apedersen00/tt6581/pcb/power.kicad_sch

## KiCad design pcb/power.kicad_sch (2026-03-07, an earlier design)

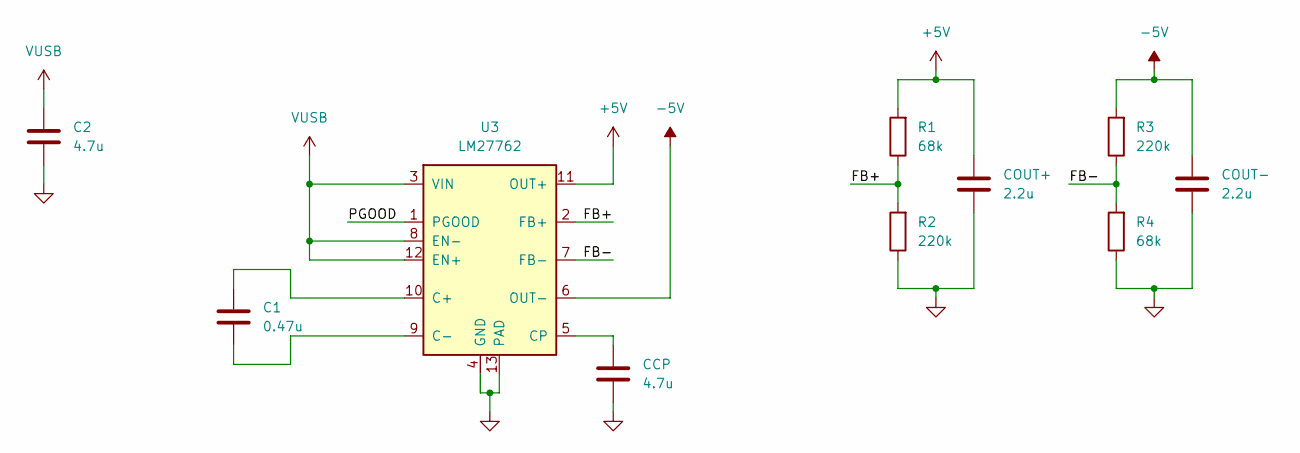
[picture p2: schematic power.kicad_sch]

Parts:
C1: 0.47u
C2: 4.7u
CCP: 4.7u
COUT+: 2.2u
COUT-: 2.2u
R1, R4: 68k
R2, R3: 220k
U3: LM27762; WSON-12-1EP_3x2mm_P0.5mm_EP1x2.65_ThermalVias

Connections:
+5V: COUT+.1, R1.2, U3.11 (OUT+)
-5V: COUT-.1, R3.2, U3.6 (OUT-)
FB+: R1.1, R2.2, U3.2 (FB+)
FB-: R3.1, R4.2, U3.7 (FB-)
GND: C2.2, CCP.2, COUT+.2, COUT-.2, R2.1, R4.1, U3.4 (GND), U3.13 (PAD)
unnamed: C1.1, U3.10 (C+)
unnamed: C1.2, U3.9 (C-)
unnamed: CCP.1, U3.5 (CP)
PGOOD: U3.1 (PGOOD)
VUSB: C2.1, U3.3 (VIN), U3.8 (EN-), U3.12 (EN+)
