apedersen00/tt6581/pcb/tt6581.kicad_sch

## KiCad design pcb/tt6581.kicad_sch (2026-03-07, an earlier design)

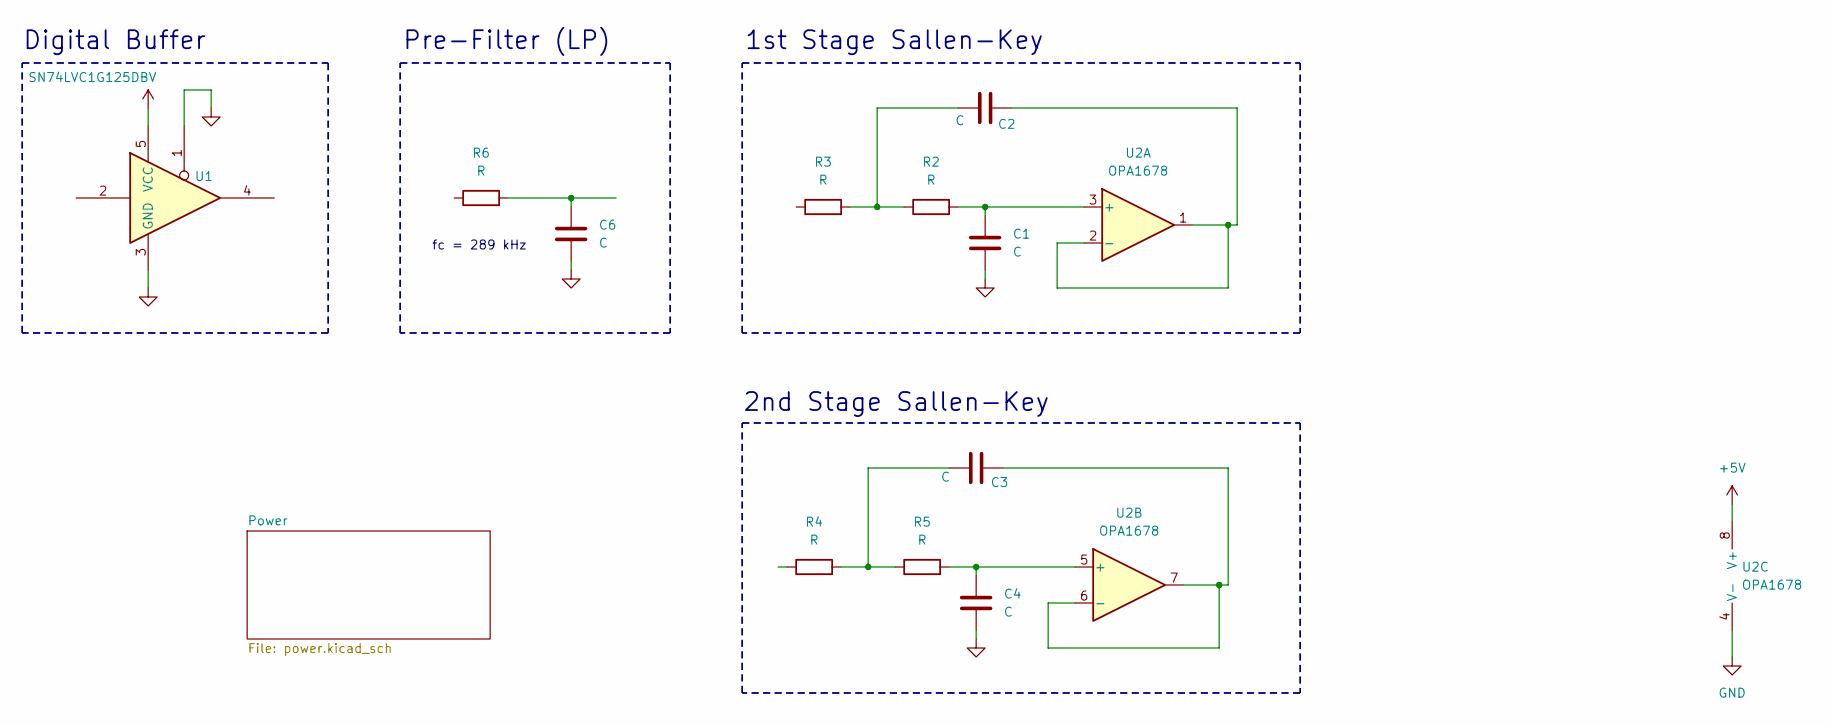
[picture p3: schematic tt6581.kicad_sch]

Parts:
C1, C2, C3, C4, C6: C
R2, R3, R4, R5, R6: R
U1: SN74LVC1G125DBV; SOT-23-5
U2: OPA1678

Connections:
+5V: U1.5 (VCC), U2.8 (V+)
GND: C1.2, C4.2, C6.2, U1.1, U1.3 (GND), U2.4 (V-)
unnamed: C1.1, R2.2, U2.3 (+)
unnamed: C2.1, R2.1, R3.2
unnamed: C2.2, U2.1, U2.2 (-)
unnamed: C3.1, R4.2, R5.1
unnamed: C3.2, U2.6 (-), U2.7
unnamed: C4.1, R5.2, U2.5 (+)
unnamed: C6.1, R6.2

Notes on the sheet:
fc = 289 kHz
Digital Buffer
Pre-Filter (LP)
1st Stage Sallen-Key
2nd Stage Sallen-Key
